pony12319/China-College-Students-Engineering-Practice-and-Innovation-Ability-Competition/决赛&国赛选拔赛/HARDWARE/COMPRESSOR/compressor.h

#ifndef __COMPRESSOR_H
#define __COMPRESSOR_H

#include "stm32f10x.h"
#include "delay.h"


void Compressor_Init(void);
void Compressor_Stop(void);
void Compressor_Forward(void);
void Compressor_Back(void);
void Compressor_Press(void);


#endif
