pony12319/China-College-Students-Engineering-Practice-and-Innovation-Ability-Competition/决赛&国赛选拔赛/VL53L0X/demo/vl53l0x.c

#include "vl53l0x.h"

//////////////////////////////////////////////////////////////////////////////////	 
//本程序只供学习使用，未经作者许可，不得用于其它任何用途
//ALIENTEK MiniV3 STM32开发板
//VL53L0X-功能测试 驱动代码	   
//正点原子@ALIENTEK
//技术论坛:www.openedv.com
//创建日期:2017/7/1
//版本：V1.0
//版权所有，盗版必究。
//Copyright(C) 广州市星翼电子科技有限公司 2009-2019
//All rights reserved									  
////////////////////////////////////////////////////////////////////////////////// 

VL53L0X_Dev_t vl53l0x_dev0;//设备I2C数据参数
VL53L0X_Dev_t vl53l0x_dev1;
VL53L0X_Dev_t vl53l0x_dev2;
VL53L0X_Dev_t vl53l0x_dev3;
u16 distancebuff[4];

VL53L0X_DeviceInfo_t vl53l0x_dev_info;//设备ID版本信息
uint8_t AjustOK=0;//校准标志位

//VL53L0X各测量模式参数
//0：默认;1:高精度;2:长距离;3:高速
mode_data Mode_data[]=
{
    {(FixPoint1616_t)(0.25*65536), 
	 (FixPoint1616_t)(18*65536),
	 33000,
	 14,
	 10},//默认
		
	{(FixPoint1616_t)(0.25*65536) ,
	 (FixPoint1616_t)(18*65536),
	 200000, 
	 14,
	 10},//高精度
		
    {(FixPoint1616_t)(0.1*65536) ,
	 (FixPoint1616_t)(60*65536),
	 33000,
	 18,
	 14},//长距离
	
    {(FixPoint1616_t)(0.25*65536) ,
	 (FixPoint1616_t)(32*65536),
	 20000,
	 14,
	 10},//高速
		
};

//API错误信息打印
//Status：详情看VL53L0X_Error参数的定义
void print_pal_error(VL53L0X_Error Status)
{
	
	char buf[VL53L0X_MAX_STRING_LENGTH];
	
	VL53L0X_GetPalErrorString(Status,buf);//根据Status状态获取错误信息字符串
	
    printf("API Status: %i : %s\r\n",Status, buf);//打印状态和错误信息
	
}

//模式字符串显示
//mode:0-默认;1-高精度;2-长距离;3-高速
void mode_string(u8 mode,char *buf)
{
	switch(mode)
	{
		case Default_Mode: strcpy(buf,"Default");        break;
		case HIGH_ACCURACY: strcpy(buf,"High Accuracy"); break;
		case LONG_RANGE: strcpy(buf,"Long Range");       break;
		case HIGH_SPEED: strcpy(buf,"High Speed");       break;
	}

}

//配置VL53L0X设备I2C地址
//dev:设备I2C参数结构体
//newaddr:设备新I2C地址
VL53L0X_Error vl53l0x_Addr_set(VL53L0X_Dev_t *dev,uint8_t newaddr)
{
	uint16_t Id;
	uint8_t FinalAddress;
	VL53L0X_Error Status = VL53L0X_ERROR_NONE;
	u8 sta=0x00;
	
	FinalAddress = newaddr;
	
	if(FinalAddress==dev->I2cDevAddr)//新设备I2C地址与旧地址一致,直接退出
		return VL53L0X_ERROR_NONE;
	//在进行第一个寄存器访问之前设置I2C标准模式(400Khz)
	Status = VL53L0X_WrByte(dev,0x88,0x00);
	if(Status!=VL53L0X_ERROR_NONE) 
	{
		sta=0x01;//设置I2C标准模式出错
		goto set_error;
	}
	//尝试使用默认的0x52地址读取一个寄存器
	Status = VL53L0X_RdWord(dev, VL53L0X_REG_IDENTIFICATION_MODEL_ID, &Id);
	if(Status!=VL53L0X_ERROR_NONE) 
	{
		sta=0x02;//读取寄存器出错
		goto set_error;
	}
	if(Id == 0xEEAA)
	{
		//设置设备新的I2C地址
		Status = VL53L0X_SetDeviceAddress(dev,FinalAddress);
		if(Status!=VL53L0X_ERROR_NONE) 
		{
			sta=0x03;//设置I2C地址出错
			goto set_error;
		}
		//修改参数结构体的I2C地址
		dev->I2cDevAddr = FinalAddress;
		//检查新的I2C地址读写是否正常
		Status = VL53L0X_RdWord(dev, VL53L0X_REG_IDENTIFICATION_MODEL_ID, &Id);
		if(Status!=VL53L0X_ERROR_NONE) 
		{
			sta=0x04;//新I2C地址读写出错
			goto set_error;
		}	
	}
	set_error:
	if(Status!=VL53L0X_ERROR_NONE)
	{
		print_pal_error(Status);//打印错误信息
	}
	if(sta!=0)
	  printf("sta:0x%x\r\n",sta);
	return Status;
}

//vl53l0x复位函数
//dev:设备I2C参数结构体
void vl53l0x_reset(VL53L0X_Dev_t *dev)
{
	uint8_t addr;
	addr = dev->I2cDevAddr;//保存设备原I2C地址
    VL53L0X_Xshut0=0;//失能VL53L0X
	delay_ms(30);
	VL53L0X_Xshut0=1;//使能VL53L0X,让传感器处于工作(I2C地址会恢复默认0X52)
	delay_ms(30);	
	dev->I2cDevAddr=0x52;
	vl53l0x_Addr_set(dev,addr);//设置VL53L0X传感器原来上电前原I2C地址
	VL53L0X_DataInit(dev);	
}

VL53L0X_Error vl53l0x_initX(VL53L0X_Dev_t *dev,u8 vl53l0_x_id)
{
	VL53L0X_Error Status = VL53L0X_ERROR_NONE;		
	VL53L0X_Dev_t *pMyDevice = dev;	
	
	pMyDevice->I2cDevAddr = VL53L0X_Addr;//I2C地址(上电默认0x52)
	pMyDevice->comms_type = 1;           //I2C通信模式
	pMyDevice->comms_speed_khz = 400;    //I2C通信速率
	
	switch(vl53l0_x_id)
	  {
		case 0:  
		   VL53L0X_Xshut0=1;
   	       delay_ms(20);
		   vl53l0x_Addr_set(pMyDevice,0x54);//设置第一个VL53L0X传感器I2C地址
		   //vl53l0x_dev0.I2cDevAddr=0x54;
		   break;
		case 1:  		     
	       VL53L0X_Xshut1=1;
   	       delay_ms(20);
		   vl53l0x_Addr_set(pMyDevice,0x56);//设置第一个VL53L0X传感器I2C地址
		   //vl53l0x_dev1.I2cDevAddr=0x56;
		   break;
		case 2:  
			VL53L0X_Xshut2=1;
   	        delay_ms(20);
		    vl53l0x_Addr_set(pMyDevice,0x58);
		    //vl53l0x_dev2.I2cDevAddr=0x58;
			break;
		case 3:  
			VL53L0X_Xshut3=1;
   	        delay_ms(20);
		    vl53l0x_Addr_set(pMyDevice,0x5a);
		    //vl53l0x_dev3.I2cDevAddr=0x5a;
			break;
	  }
    if(Status!=VL53L0X_ERROR_NONE) goto error;
	Status = VL53L0X_DataInit(pMyDevice);//设备初始化
	if(Status!=VL53L0X_ERROR_NONE) goto error;
	delay_ms(2);
	Status = VL53L0X_GetDeviceInfo(pMyDevice,&vl53l0x_dev_info);//获取设备ID信息
    if(Status!=VL53L0X_ERROR_NONE) goto error;
		
	  AjustOK=0;
	
	error:
	if(Status!=VL53L0X_ERROR_NONE)
	{
		print_pal_error(Status);//打印错误信息
		return Status;
	}
}

//初始化vl53l0x
//dev:设备I2C参数结构体
VL53L0X_Error vl53l0x_init()
{	
	VL53L0X_Error Status = VL53L0X_ERROR_NONE;	
	VL53L0X_i2c_init();//初始化IIC总线
	
	Status=vl53l0x_initX(&vl53l0x_dev0,0);
	if(Status!=0) return Status;
	
	Status=vl53l0x_initX(&vl53l0x_dev1,1);
	if(Status!=0) return Status;
	
	Status=vl53l0x_initX(&vl53l0x_dev2,2);
	if(Status!=0) return Status;
	
	Status=vl53l0x_initX(&vl53l0x_dev3,3);
	if(Status!=0) return Status;
  
}

u8 mode=0;//VL53L0x工作模式设置--2019/11/12
void all_vl53l0x_init()
{
	if(vl53l0x_init())     //vl53l0x初始化
	 {
		printf("VL53L0X_Init Error!!!\r\n");
		delay_ms(200);
	 }
	 else
	 { 
		 printf("VL53L0X_Init OK\r\n");
		 delay_ms(200);
	 }

	if(vl53l0x_set_mode(&vl53l0x_dev0,mode)&&vl53l0x_set_mode(&vl53l0x_dev1,mode)
		  &&vl53l0x_set_mode(&vl53l0x_dev2,mode)&&vl53l0x_set_mode(&vl53l0x_dev3,mode))   //配置测量模式
		{
			printf("Mode Set Error!!!\r\n");
		}
	else
		printf("Mode Set OK!!!\r\n");
	delay_ms(200);
}

void vl53l0x_getdistance()
{
	VL53L0X_Error Status=VL53L0X_ERROR_NONE;//VL53L0x工作状态
	static char buf[VL53L0X_MAX_STRING_LENGTH];//测试模式字符串字符缓冲区
	
	Status = vl53l0x_start_single_test(&vl53l0x_dev0,&vl53l0x_data,buf);//执行一次测量
	if(Status==VL53L0X_ERROR_NONE)
		//printf("d0: %4imm%x\r\n",Distance_data,vl53l0x_dev0.I2cDevAddr);//打印测量距离
	       distancebuff[0]=Distance_data;
	else
		delay_ms(1);
//		printf("Measurement d0 is Error!!!\r\n");	
	//delay_ms(10);
	
	Status = vl53l0x_start_single_test(&vl53l0x_dev1,&vl53l0x_data,buf);//执行一次测量
	if(Status==VL53L0X_ERROR_NONE)
		   distancebuff[1]=Distance_data;
	else
		delay_ms(1);
//		printf("Measurement d1 is Error!!!\r\n");	
	//delay_ms(10);
	
	Status = vl53l0x_start_single_test(&vl53l0x_dev2,&vl53l0x_data,buf);//执行一次测量
	if(Status==VL53L0X_ERROR_NONE)
		distancebuff[2]=Distance_data;
	else
		delay_ms(1);
//		printf("Measurement d2 is Error!!!\r\n");	
	//delay_ms(10);
	
	Status = vl53l0x_start_single_test(&vl53l0x_dev3,&vl53l0x_data,buf);//执行一次测量
	if(Status==VL53L0X_ERROR_NONE)
		distancebuff[3]=Distance_data;
	else
		delay_ms(1);
//		printf("Measurement d3 is Error!!!\r\n");	
	//delay_ms(1000);
}
/*
//VL53L0X主测试程序
void vl53l0x_test(void)
{
	 while(vl53l0x_init(&vl53l0x_dev))//vl53l0x初始化
	 {
		printf("VL53L0X_Init Error!!!\r\n");
		delay_ms(500);
	 }
	 printf("VL53L0X_Init OK\r\n");
	 
	 while(1)
	 {
		 //	vl53l0x_calibration_test(&vl53l0x_dev);   break;//校准模式
		 //vl53l0x_general_test(&vl53l0x_dev);       break;//普通测量模式
		 //vl53l0x_interrupt_test(&vl53l0x_dev);     break;//中断测量模式  
		 vl53l0x_general_test(&vl53l0x_dev);
		 delay_ms(500);
	 }
}
*/
//----------以下函数为USMART调用------------//

//获取vl53l0x传感器ID信息
void vl53l0x_info(void)
{
	printf("\r\n-------vl53l0x传感器设备信息-------\r\n\r\n");
	printf("  Name:%s\r\n",vl53l0x_dev_info.Name);
	printf("  Addr:0x%x\r\n",vl53l0x_dev0.I2cDevAddr);
	printf("  ProductId:%s\r\n",vl53l0x_dev_info.ProductId);
	printf("  RevisionMajor:0x%x\r\n",vl53l0x_dev_info.ProductRevisionMajor);
	printf("  RevisionMinor:0x%x\r\n",vl53l0x_dev_info.ProductRevisionMinor);
	printf("\r\n-----------------------------------\r\n");
}

//获取一次测量距离数据
//mode模式配置 0:默认;1:高精度;2:长距离;3:高速
void One_measurement(u8 mode)
{
	vl53l0x_set_mode(&vl53l0x_dev0,mode);
	VL53L0X_PerformSingleRangingMeasurement(&vl53l0x_dev0,&vl53l0x_data);
	printf("\r\n d: %4d mm.\r\n",vl53l0x_data.RangeMilliMeter);
		
}
