pony12319/China-College-Students-Engineering-Practice-and-Innovation-Ability-Competition/决赛&国赛选拔赛/VL53L0X/demo/vl53l0x.h

#ifndef __VL53L0X_H
#define __VL53L0X_H

#include "vl53l0x_api.h"
#include "vl53l0x_platform.h"
#include "vl53l0x_gen.h"
#include "vl53l0x_cali.h"
#include "vl53l0x_it.h"
#include "sys.h"
#include "delay.h"

//////////////////////////////////////////////////////////////////////////////////	 
//本程序只供学习使用，未经作者许可，不得用于其它任何用途
//ALIENTEK MiniV3 STM32开发板
//VL53L0X-功能测试 驱动代码	   
//正点原子@ALIENTEK
//技术论坛:www.openedv.com
//创建日期:2017/7/1
//版本：V1.0
//版权所有，盗版必究。
//Copyright(C) 广州市星翼电子科技有限公司 2009-2019
//All rights reserved									  
////////////////////////////////////////////////////////////////////////////////// 

//VL53L0X传感器上电默认IIC地址为0X52(不包含最低位)
#define VL53L0X_Addr 0x52

//控制Xshut电平,从而使能VL53L0X工作 1:使能 0:关闭
#define VL53L0X_Xshut0 PFout(2)
#define VL53L0X_Xshut1 PFout(3)
#define VL53L0X_Xshut2 PFout(4)
#define VL53L0X_Xshut3 PFout(5)


//使能2.8V IO电平模式
#define USE_I2C_2V8  1

//测量模式
#define Default_Mode   0// 默认
#define HIGH_ACCURACY  1//高精度
#define LONG_RANGE     2//长距离
#define HIGH_SPEED     3//高速

//vl53l0x模式配置参数集
typedef __packed struct
{
	FixPoint1616_t signalLimit;    //Signal极限数值 
	FixPoint1616_t sigmaLimit;     //Sigmal极限数值
	uint32_t timingBudget;         //采样时间周期
	uint8_t preRangeVcselPeriod ;  //VCSEL脉冲周期
	uint8_t finalRangeVcselPeriod ;//VCSEL脉冲周期范围
	
}mode_data;


extern mode_data Mode_data[];
extern uint8_t AjustOK;
extern u16 distancebuff[4];

VL53L0X_Error vl53l0x_init();//初始化vl53l0x
void print_pal_error(VL53L0X_Error Status);//错误信息打印
void mode_string(u8 mode,char *buf);//模式字符串显示
void vl53l0x_test(void);//vl53l0x测试
void vl53l0x_reset(VL53L0X_Dev_t *dev);//vl53l0x复位

void all_vl53l0x_init();
void vl53l0x_getdistance();


void vl53l0x_info(void);//获取vl53l0x设备ID信息
void One_measurement(u8 mode);//获取一次测量距离数据
#endif
